KiloanTV/Kiloan-ADM/images/input-buffer-example.png

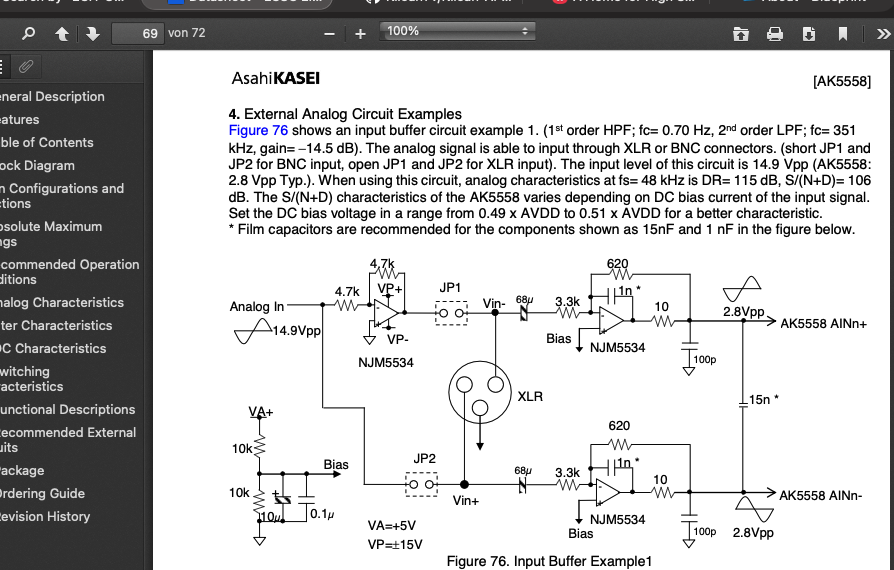
images/input-buffer-example.png
